Aurelio92/GCPlus-2.0/GCPlus2.0.X/nvm.c

#include "main.h"

void NVMUnlock(void) {
    uint8_t gie = INTCON0bits.GIE;
    INTCON0bits.GIE = 0;
    NVMCON2 = 0x55;
    NVMCON2 = 0xAA;
    NVMCON1bits.WR = 1;
    INTCON0bits.GIE = gie;
}

uint8_t EEPROMReadByte(uint8_t address) {
    NVMCON1 = 0;
    NVMADRL = address;
    NVMCON1bits.RD = 1;
    return NVMDAT;
}

void EEPROMWriteByte(uint8_t address, uint8_t data) {
    NVMCON1 = 0;
    NVMADRL = address;
    NVMDAT = data;
    NVMCON1bits.WREN = 1;
    NVMUnlock();
    while (NVMCON1bits.WR);
    NVMCON1bits.WREN = 0;
}
